jdohm/ZP_Muelleimer/pictures/simple_bot-advanced_top.jpg

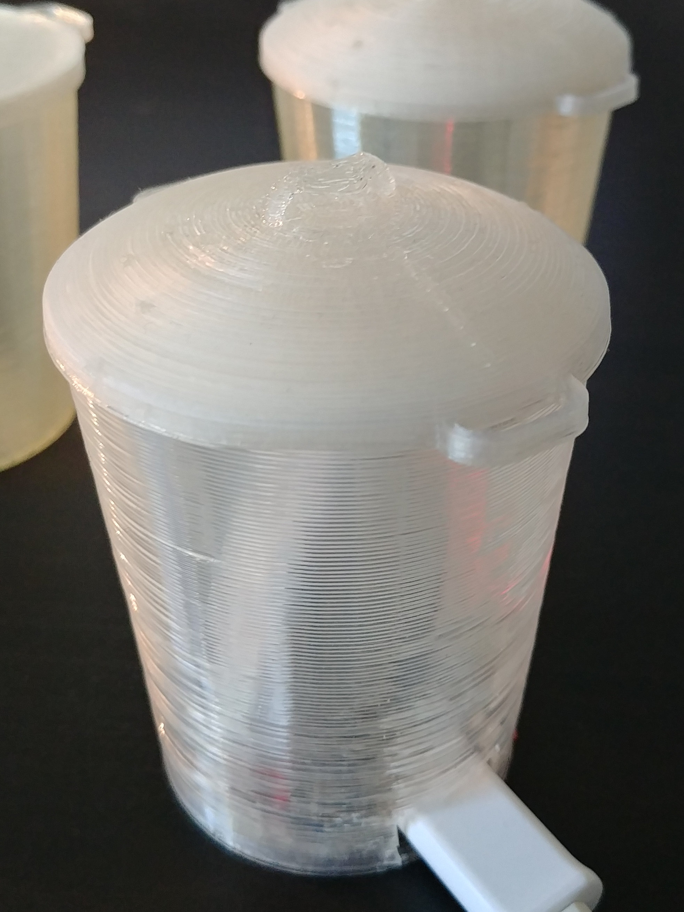
pictures/simple_bot-advanced_top.jpg
