jdohm/ZP_Muelleimer/pictures/tonnen.jpg

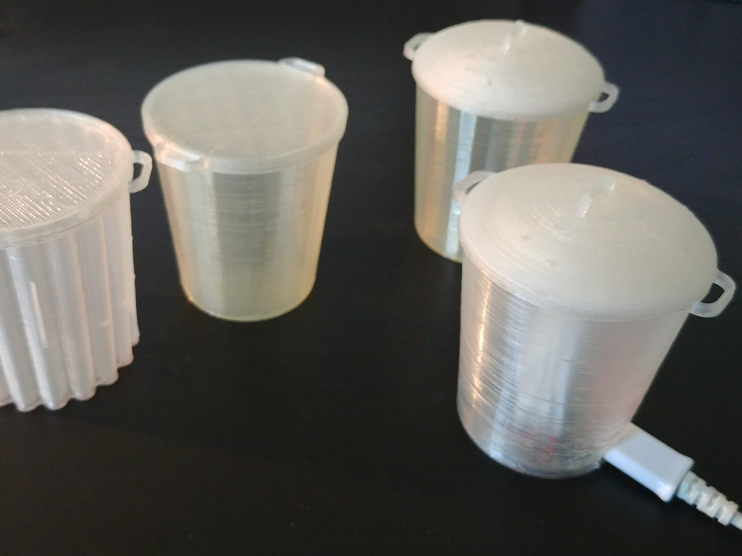
pictures/tonnen.jpg
