jdohm/ZP_Muelleimer/pictures/tonnen_2.jpg

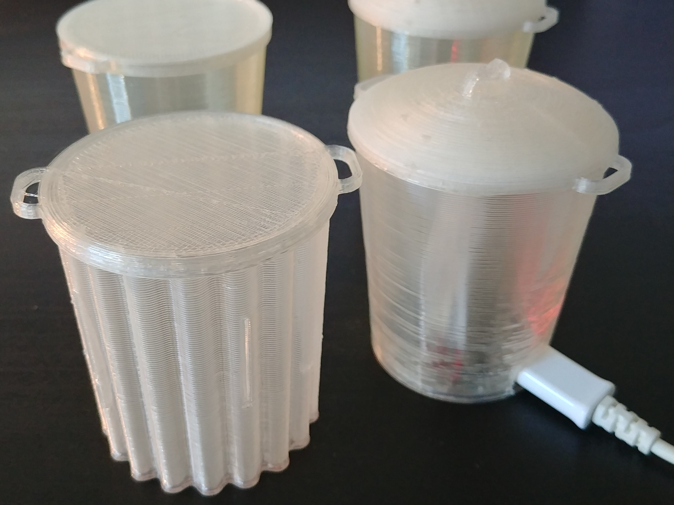
pictures/tonnen_2.jpg
