jdohm/ZP_Muelleimer/software/Velbert_https/VelbertMuellParser.h

/*
  VelbertMuellParser.h - 
  The aim of this library is, to enable you to easily search for words in the event description on given days.
  This will be used to evaluate if tomorrow the trash will be emtied. 
  So that an output can signal to put out the trash.
  Created by Jannis Dohm, 2020-02-12.
  Released under MIT License.
*/
#ifndef VelbertMuellParser_
#define VelbertMuellParser_

#include "Arduino.h"

class VelbertMuellParser
{
    public:
        VelbertMuellParser(char *DatabaseURL);
        void SetStreet(String Street);
        bool CheckDate(char* SearchFor, int day, int month, int year);

    private:
        char *_DatabaseURL;
        String _Street;
        String _ToTwoString(int Number);
};


#endif //VelbertMuellParser_
